oskitone/space_dice/openscad/space_dice.scad

include <../../parts_cafe/openscad/battery-9v.scad>;
include <../../parts_cafe/openscad/knob.scad>;
include <../../parts_cafe/openscad/nuts_and_bolts.scad>;
include <../../parts_cafe/openscad/print_test.scad>;
include <../../parts_cafe/openscad/speaker-AZ40R.scad>;
include <../../parts_cafe/openscad/switch_clutch-angled.scad>;
include <../../parts_cafe/openscad/switch_clutch.scad>;

include <battery_cover.scad>;
include <button_lever.scad>;
include <enclosure.scad>;
include <led_display.scad>;
include <pcb.scad>;

module space_dice(
    width = ENCLOSURE_DIMENSIONS.x,
    length = ENCLOSURE_DIMENSIONS.y,
    height = ENCLOSURE_DIMENSIONS.z,

    pcb_width = PCB_WIDTH,
    pcb_length = PCB_LENGTH,

    show_enclosure_bottom = true,
    show_battery = true,
    show_battery_cover = true,
    show_pcb = true,
    show_knobs = true,
    show_button_actuator_mount = true,
    show_button_cap = true,
    show_side_switch_clutch = true,
    show_top_switch_clutches = true,
    show_speaker = true,
    show_led_display = true,
    show_nuts_and_bolts = true,
    show_enclosure_top = true,
    show_print_test = false,

    show_clearance = false,

    side_switch_exposed_width = 2,
    top_switch_exposed_height = 4,
    button_exposed_height = 6,
    knob_exposed_height = 8,

    switch_clearance = .3,
    knob_clearance = .5,
    control_z_clearance = .4,

    button_lever_arm_height = 2,
    knob_brim_coverage = .6,

    control_width = CONTROL_WIDTH,
    control_length = CONTROL_LENGTH,

    outer_gutter = OUTER_GUTTER,
    default_gutter = SCOUT_DEFAULT_GUTTER,

    accessory_fillet = 1,

    pcb_top_clearance = PCB_TOP_CLEARANCE,
    pcb_bottom_clearance = PCB_BOTTOM_CLEARANCE,

    pcb_screw_hole_position = PCB_HOLE_POSITIONS[4],
    pcb_post_hole_positions = [
        PCB_HOLE_POSITIONS[0],
        PCB_HOLE_POSITIONS[2],
        PCB_HOLE_POSITIONS[3],
        PCB_HOLE_POSITIONS[6],
    ],

    tolerance = 0,

    enclosure_outer_color = "#FF69B4",
    enclosure_cavity_color = "#CC5490",

    control_outer_color = "#FFFFFF",
    control_cavity_color = "#EEEEEE",

    led_display_color = "#FFFFFF",

    side_switch_position = round($t),

    // NOTE: eyeballed!
    switch_clutch_web_length_extension = 4,
    switch_clutch_overshoot = [0, 1],

    quick_preview = true
) {
    e = .0319;

    available_width = width - outer_gutter * 2;
    available_length = length - outer_gutter * 2;

    speaker_z = ENCLOSURE_FLOOR_CEILING - ENCLOSURE_ENGRAVING_DEPTH;
    pcb_position = [
        PCB_XY,
        PCB_XY,
        speaker_z + SPEAKER_HEIGHT + pcb_bottom_clearance
    ];
    speaker_position = [
        pcb_position.x + pcb_screw_hole_position.x / 2,
        pcb_position.y + pcb_length / 2,
        speaker_z
    ];

    battery_position = [
        width - ENCLOSURE_WALL - BATTERY_HEIGHT - e,
        ENCLOSURE_WALL + e,
        ENCLOSURE_FLOOR_CEILING
    ];

    switch_clutch_grip_height = height / 2;

    enclosure_bottom_height = pcb_position.z - ENCLOSURE_LIP_HEIGHT + PCB_HEIGHT;
    enclosure_top_height = height - enclosure_bottom_height;

    knob_diameter = CONTROL_WIDTH - knob_clearance * 2;
    knob_brim_diameter = CONTROL_WIDTH + knob_brim_coverage;

    right_panel_width = width
        - outer_gutter * 2 - default_gutter * 3
        - control_width * 3;
    right_panel_third_length =
        (length - outer_gutter * 2 - default_gutter * 2) / 3;
    branding_dimensions = [right_panel_width, right_panel_third_length];
    speaker_grill_dimensions = [ right_panel_width, right_panel_third_length];
    button_cap_exposure_dimensions = [right_panel_width, right_panel_third_length];

    branding_position = [
        width - outer_gutter - right_panel_width,
        length - outer_gutter - branding_dimensions.y
    ];
    speaker_grill_position = [
        width - outer_gutter - right_panel_width,
        outer_gutter,
    ];
    button_cap_exposure_position = [
        width - outer_gutter - right_panel_width,
        outer_gutter +
            speaker_grill_dimensions.y + default_gutter,
    ];

    switch_clutch_width = control_width / 2 + switch_clutch_overshoot.x * 2;
    switch_clutch_length = control_width + SWITCH_ACTUATOR_TRAVEL + switch_clutch_overshoot.y * 2;

    echo("Enclosure", width / 25.4, length / 25.4, height / 25.4);
    echo("PCB", pcb_width / 25.4, pcb_length / 25.4);
    echo("PCB bottom clearance", pcb_position.z - ENCLOSURE_FLOOR_CEILING);
    echo("Speaker",
        SPEAKER_DIAMETER / 2,
        get_speaker_fixture_diameter(tolerance),
        [
            // consts here are bottom left of PCB in KiCad
            (speaker_position.x - pcb_position.x) + 101.6,
            114.3 - (speaker_position.y - pcb_position.y),
        ]
    );
    echo("Knob bottom diameter", knob_brim_diameter);
    echo("Top switch clutches", switch_clutch_width, switch_clutch_length,
        switch_clutch_length + SWITCH_ACTUATOR_TRAVEL);

    minimum_height = pcb_position.z + PCB_HEIGHT + pcb_top_clearance
        + ENCLOSURE_FLOOR_CEILING;
    assert(height >= minimum_height, "Height is too low.");

    if (show_battery) {
        translate(battery_position) translate([0, 0, -e]) {
            rotate([0, 90, 0]) rotate([0, 0, 90])
            % battery();
        }
    }

    if (show_battery_cover) {
        battery_cover_position = [
            battery_position.x,
            ENCLOSURE_WALL + tolerance,
            battery_position.z + BATTERY_LENGTH
        ];

        battery_cover_dimensions = [
            BATTERY_HEIGHT,
            (speaker_grill_position.y - ENCLOSURE_WALL) * 2
                + speaker_grill_dimensions.y,
            BATTERY_COVER_HEIGHT
        ];

        translate(battery_cover_position) {
            battery_cover(
                dimensions = battery_cover_dimensions,
                outer_color = control_outer_color
            );
        }
    }

    if (show_enclosure_bottom || show_enclosure_top) {
        enclosure(
            show_top = show_enclosure_top,
            show_bottom = show_enclosure_bottom,

            dimensions = [width, length, height],
            bottom_height = enclosure_bottom_height,
            top_height = enclosure_top_height,

            pcb_position = pcb_position,

            speaker_position = speaker_position,

            pcb_width = pcb_width,
            pcb_length = pcb_length,

            pcb_screw_hole_positions = [pcb_screw_hole_position],
            pcb_post_hole_positions = pcb_post_hole_positions,

            switch_clutch_grip_height = switch_clutch_grip_height,
            switch_clutch_web_length_extension = switch_clutch_web_length_extension,

            right_panel_width = right_panel_width,
            branding_dimensions = branding_dimensions,
            speaker_grill_dimensions = speaker_grill_dimensions,
            branding_position = branding_position,
            speaker_grill_position = speaker_grill_position,
            button_cap_exposure_dimensions = button_cap_exposure_dimensions,
            button_cap_exposure_position = button_cap_exposure_position,
            button_lever_arm_height = button_lever_arm_height,

            outer_gutter = outer_gutter,
            default_gutter = default_gutter,

            tolerance = tolerance,

            outer_color = enclosure_outer_color,
            cavity_color = enclosure_cavity_color,

            show_dfm = !quick_preview,

            quick_preview = quick_preview
        );
    }

    translate(pcb_position) translate([0, 0, -e]) {
        pcb(
            show_board = show_pcb,
            show_silkscreen = false,

            show_switches = show_pcb,
            show_leds = show_pcb,
            show_pots = show_pcb,
            show_button = show_pcb,

            show_clearance = show_clearance,

            side_switch_position = side_switch_position,

            tolerance = tolerance
        );
    }

    if (show_knobs) {
        knob_z = pcb_position.z + PCB_HEIGHT + PTV09A_POT_BASE_HEIGHT_FROM_PCB + control_z_clearance;
        knob_min_height = PTV09A_POT_ACTUATOR_HEIGHT - control_z_clearance
            + ENCLOSURE_FLOOR_CEILING;
        knob_height = height - knob_z + knob_exposed_height;

        assert(
            knob_height > knob_min_height,
            "Knobs aren't tall enough to conceal pot shaft."
        );

        for (xy = PCB_POT_POSITIONS) {
            translate([
                pcb_position.x + xy.x,
                pcb_position.y + xy.y,
                knob_z
            ]) {
                knob(
                    diameter = knob_diameter,
                    height = knob_height,
                    fillet = accessory_fillet,
                    dimple_y = knob_diameter / 2 / 2,
                    round_bottom = false,
                    brim_diameter = knob_brim_diameter,
                    brim_height =
                        height - ENCLOSURE_FLOOR_CEILING - knob_z - control_z_clearance,
                    color = "#FFFFFF",
                    cavity_color = "#EEEEEE",
                    tolerance = tolerance,
                    $fn = quick_preview ? undef : 24
                );
            }
        }
    }

    if (show_button_actuator_mount || show_button_cap) {
        color(control_outer_color) {
            button_lever(
                pcb_position = pcb_position,
                screw_mount_position = [
                    pcb_position.x + pcb_screw_hole_position.x,
                    pcb_position.y + pcb_screw_hole_position.y
                ],
                battery_position = battery_position,
                exposure_position = button_cap_exposure_position,
                exposure_dimensions = button_cap_exposure_dimensions,
                knob_brim_diameter = knob_brim_diameter,
                control_clearance = switch_clearance,
                arm_height = button_lever_arm_height,
                fillet = accessory_fillet,
                tolerance = tolerance,
                actuator_mount_z = pcb_position.z + PCB_HEIGHT,
                exposed_height = button_exposed_height,
                chamfer = accessory_fillet,
                show_cap = show_button_cap,
                show_actuator_mount = show_button_actuator_mount,
                $fn = quick_preview ? undef : 12
            );
        }
    }

    if (show_side_switch_clutch) {
        // HACK: lots of arbitrary values here to make Scout's clutch work.
        // Copied from higher_lower bahhhhh
        translate([
            pcb_position.x + SWITCH_ORIGIN.x + .15,
            pcb_position.y + PCB_SWITCH_Y + SWITCH_ORIGIN.y,
            0
        ]) {
            switch_clutch_angled(
                position = side_switch_position,

                web_available_width = pcb_position.x - ENCLOSURE_WALL,
                web_length_extension = switch_clutch_web_length_extension,

                enclosure_height = height,
                vertical_clearance = control_z_clearance,

                // Negative here to make up for bigger tolerance below
                x_clearance = -.2,

                grip_height = switch_clutch_grip_height,

                switch_actuator_width = 4,

                fillet = accessory_fillet,
                side_overexposure = side_switch_exposed_width,
                tolerance = tolerance * 2, // NOTE: intentionally loose

                outer_color = control_outer_color,
                cavity_color = control_cavity_color,

                quick_preview = 0
            );
        }
    }

    if (show_top_switch_clutches) {
        top_switch_clutch_z = pcb_position.z + PCB_HEIGHT + SWITCH_BASE_HEIGHT;

        for (i = [0 : len(PCB_TOP_CONTROL_SWITCH_POSITONS) - 1]) {
            xy = PCB_TOP_CONTROL_SWITCH_POSITONS[i];

            translate([
                pcb_position.x + xy.x,
                pcb_position.y + xy.y,
                top_switch_clutch_z - e
            ]) {
                switch_clutch(
                    base_width = SWITCH_CLUTCH_MIN_BASE_WIDTH,
                    base_length = SWITCH_CLUTCH_MIN_BASE_LENGTH,
                    base_height = height - top_switch_clutch_z
                        - ENCLOSURE_FLOOR_CEILING - control_z_clearance,

                    plate_width = switch_clutch_width,
                    plate_length = switch_clutch_length,
                    plate_height = ENCLOSURE_FLOOR_CEILING,

                    actuator_width = control_width / 2
                        - switch_clearance * 2,
                    actuator_length = control_width - SWITCH_ACTUATOR_TRAVEL
                        - switch_clearance * 2,
                    actuator_height = ENCLOSURE_FLOOR_CEILING
                        + top_switch_exposed_height + control_z_clearance,

                    position = 1,

                    cavity_base_height = -e,
                    cavity_actuator_height = SWITCH_ACTUATOR_HEIGHT + e,

                    fillet = accessory_fillet,

                    color = control_outer_color,
                    cavity_color = control_cavity_color,

                    chamfer_cavity_top = false,
                    chamfer_cavity_entrance = true,

                    tolerance = tolerance
                );
            }
        }
    }

    if (show_speaker) {
        % translate([
            speaker_position.x,
            speaker_position.y,
            speaker_position.z - e * 2
        ]) {
            speaker($fn = 120);
        }
    }

    if (show_led_display) {
        exposure_position = [
            outer_gutter + (control_width + default_gutter) * 2,
            outer_gutter,
            pcb_position.z + PCB_HEIGHT
        ];

        translate(exposure_position) {
            led_display(
                exposed_width = control_width,
                exposed_length = control_length,
                exposed_height = accessory_fillet,
                inner_height = height - ENCLOSURE_FLOOR_CEILING
                    - exposure_position.z,
                fillet = accessory_fillet,
                tolerance = tolerance,
                outer_color = control_outer_color,
                cavity_color = control_cavity_color,
                accent_color = enclosure_cavity_color,
                $fn = quick_preview ? undef : 12
            );
        }
    }

    if (show_nuts_and_bolts) {
        screw_length = 1/2 * 25.4;
        screw_z = pcb_position.z + PCB_HEIGHT
            + BUTTON_LEVER_ACTUATOR_MOUNT_HEIGHT
            - screw_length;

        translate([
            pcb_position.x + pcb_screw_hole_position.x,
            pcb_position.y + pcb_screw_hole_position.y,
            pcb_position.z - PCB_BOTTOM_MIN_CLEARANCE - PCB_MOUNT_POST_CEILING
                - NUT_HEIGHT
        ]) {
            % nut();
        }

        % screws(
            positions = [pcb_screw_hole_position],
            pcb_position = pcb_position,
            length = screw_length,
            head_on_bottom = false,
            z = screw_z
        );
    }

    if (show_print_test) {
        print_test(quick_preview = quick_preview);
    }
}

SHOW_ENCLOSURE_BOTTOM = true;
SHOW_BATTERY = true;
SHOW_BATTERY_COVER = true;
SHOW_PCB = true;
SHOW_KNOBS = true;
SHOW_BUTTON_ACTUATOR_MOUNT = true;
SHOW_BUTTON_CAP = true;
SHOW_SIDE_SWITCH_CLUTCH = true;
SHOW_TOP_SWITCH_CLUTCHES = true;
SHOW_SPEAKER = true;
SHOW_LED_DISPLAY = true;
SHOW_NUTS_AND_BOLTS = true;
SHOW_ENCLOSURE_TOP = true;
SHOW_PRINT_TEST = false;

SHOW_CLEARANCE = false;
DEFAULT_TOLERANCE = .1;
X_ROTATION = 0;
Y_ROTATION = 0;

rotate([X_ROTATION, Y_ROTATION, 0])
difference() {
space_dice(
    show_enclosure_bottom = SHOW_ENCLOSURE_BOTTOM,
    show_battery = SHOW_BATTERY,
    show_battery_cover = SHOW_BATTERY_COVER,
    show_pcb = SHOW_PCB,
    show_knobs = SHOW_KNOBS,
    show_button_actuator_mount = SHOW_BUTTON_ACTUATOR_MOUNT,
    show_button_cap = SHOW_BUTTON_CAP,
    show_side_switch_clutch = SHOW_SIDE_SWITCH_CLUTCH,
    show_top_switch_clutches = SHOW_TOP_SWITCH_CLUTCHES,
    show_speaker = SHOW_SPEAKER,
    show_led_display = SHOW_LED_DISPLAY,
    show_nuts_and_bolts = SHOW_NUTS_AND_BOLTS,
    show_enclosure_top = SHOW_ENCLOSURE_TOP,
    show_print_test = SHOW_PRINT_TEST,

    show_clearance = SHOW_CLEARANCE,

    tolerance = DEFAULT_TOLERANCE,

    quick_preview = $preview
);

// INCR
// translate([31, -1, -1]) cube([100, 100, 100]);

// VOL
// translate([55, -1, -1]) cube([100, 100, 100]);

// pcb_mount_post
// translate([52, -1, -1]) cube([100, 100, 100]);
// translate([-1, -1, -1]) cube([100, 35, 100]);

// right panel
// translate([79, -1, -1]) cube([100, 100, 100]);

// button lever
// translate([-1, -1, -1]) cube([100, 31, 100]);

// LED display
// translate([51.2, -1, -1]) cube([100, 100, 100]);

// speaker
// translate([28.2, -1, -1]) cube([100, 100, 100]);

// branding engraving
// translate([-1, -1, -1]) cube([64, 100, 100]);
// translate([-1, -1, -1]) cube([100, 39, 100]);
// translate([-1, -1, -1]) cube([100, 100, 20]);

// lever fixture subsection
// translate([-1, -1, -1]) cube([64, 100, 100]);
// translate([-1, -1, -1]) cube([100, 19, 100]);
// translate([-1, 43, -1]) cube([100, 19, 100]);
// translate([-1, -1, -1]) cube([100, 100, 19]);
}
